NoseFa/DIY-TRMNL-DASHBOARD/WiringDiagram/NordicTrmnl.kicad_sch

## KiCad design WiringDiagram/NordicTrmnl.kicad_sch (2026-04-13)

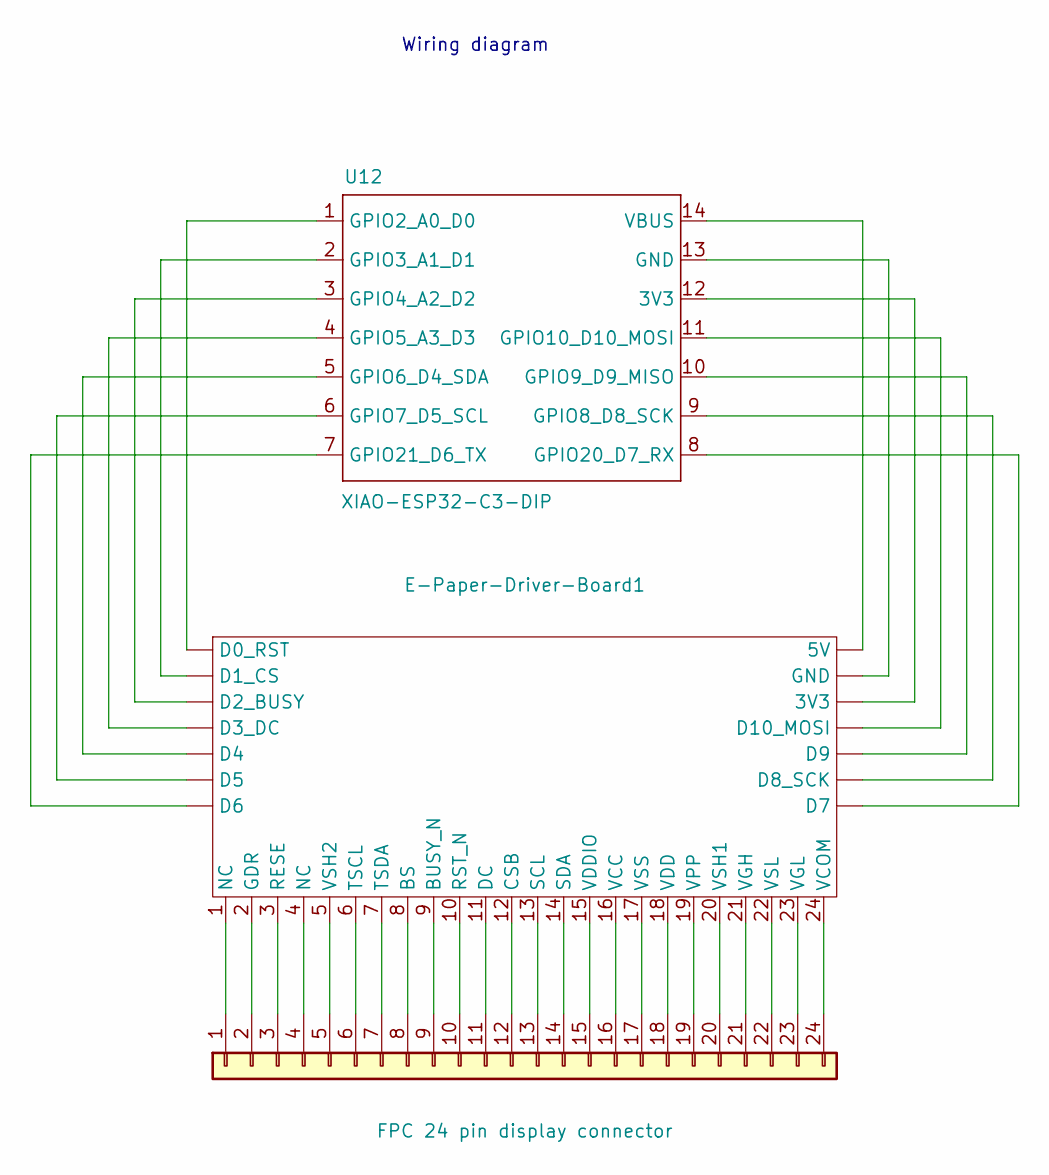
[picture p18: schematic NordicTrmnl.kicad_sch]

Parts:
E-Paper-Driver-Board1: (no value)
J1: FPC 24 pin display connector
U12: XIAO-ESP32-C3-DIP

Connections:
unnamed: E-Paper-Driver-Board1.1 (NC), J1.1
unnamed: E-Paper-Driver-Board1.2 (GDR), J1.2
unnamed: E-Paper-Driver-Board1.3 (RESE), J1.3
unnamed: E-Paper-Driver-Board1.4 (NC), J1.4
unnamed: E-Paper-Driver-Board1.5 (VSH2), J1.5
unnamed: E-Paper-Driver-Board1.6 (TSCL), J1.6
unnamed: E-Paper-Driver-Board1.7 (TSDA), J1.7
unnamed: E-Paper-Driver-Board1.8 (BS), J1.8
unnamed: E-Paper-Driver-Board1.9 (BUSY_N), J1.9
unnamed: E-Paper-Driver-Board1.10 (RST_N), J1.10
unnamed: E-Paper-Driver-Board1.11 (DC), J1.11
unnamed: E-Paper-Driver-Board1.12 (CSB), J1.12
unnamed: E-Paper-Driver-Board1.13 (SCL), J1.13
unnamed: E-Paper-Driver-Board1.14 (SDA), J1.14
unnamed: E-Paper-Driver-Board1.15 (VDDIO), J1.15
unnamed: E-Paper-Driver-Board1.16 (VCC), J1.16
unnamed: E-Paper-Driver-Board1.17 (VSS), J1.17
unnamed: E-Paper-Driver-Board1.18 (VDD), J1.18
unnamed: E-Paper-Driver-Board1.19 (VPP), J1.19
unnamed: E-Paper-Driver-Board1.20 (VSH1), J1.20
unnamed: E-Paper-Driver-Board1.21 (VGH), J1.21
unnamed: E-Paper-Driver-Board1.22 (VSL), J1.22
unnamed: E-Paper-Driver-Board1.23 (VGL), J1.23
unnamed: E-Paper-Driver-Board1.24 (VCOM), J1.24
unnamed: E-Paper-Driver-Board1. (D0_RST), U12.1 (GPIO2_A0_D0), U12.2 (GPIO3_A1_D1), U12.3 (GPIO4_A2_D2), U12.4 (GPIO5_A3_D3), U12.5 (GPIO6_D4_SDA), U12.6 (GPIO7_D5_SCL), U12.7 (GPIO21_D6_TX), U12.8 (GPIO20_D7_RX), U12.9 (GPIO8_D8_SCK), U12.10 (GPIO9_D9_MISO), U12.11 (GPIO10_D10_MOSI), U12.12 (3V3), U12.13 (GND), U12.14 (VBUS)

Notes on the sheet:
Wiring diagram
